prajjwalprajjwal/Click/firmware/src/applets/clicker/ClickerConfig.h

#ifndef CLICKER_CONFIG_H
#define CLICKER_CONFIG_H

#ifndef CLICKER_DEBUG
#define CLICKER_DEBUG 0
#endif

#define CLICKER_PERSIST_IDLE_DELAY_MS 1000
#define CLICKER_PERSIST_EVERY_N_CLICKS 20
#define CLICKER_PERSIST_MAX_INTERVAL_MS 0

#define CLICKER_NVS_NAMESPACE "clicker"
#define CLICKER_NVS_KEY_COUNT_STR "cnt_str"
#define CLICKER_NVS_KEY_TERRAIN_OFFSET "terrain_off"
#define CLICKER_NVS_KEY_LIFETIME_LO "lifetime_lo"
#define CLICKER_NVS_KEY_LIFETIME_HI "lifetime_hi"
#define CLICKER_NVS_KEY_COMPLETED_CYCLES "cycles"
#define CLICKER_NVS_KEY_MILESTONES "milestones"
#define CLICKER_NVS_KEY_HOME_UNLOCKS "home_unlocks"
#define CLICKER_NVS_KEY_LAST_CYCLE "last_cycle"
#define CLICKER_NVS_KEY_LAST_CYCLE_HI "last_cycle_hi"

#define CLICKER_CYCLE_LENGTH 100000ULL

#endif // CLICKER_CONFIG_H
