prajjwalprajjwal/Click/firmware/src/applets/clicker/SisyphusSprites.h

#ifndef SISYPHUS_SPRITES_H
#define SISYPHUS_SPRITES_H

#include <Arduino.h>

// Sprite Dimensions
#define SISYPHUS_IDLE_WIDTH 20
#define SISYPHUS_IDLE_HEIGHT 30

#define SISYPHUS_REST_WIDTH 26
#define SISYPHUS_REST_HEIGHT 27

#define SISYPHUS_PUSH_WIDTH 27
#define SISYPHUS_PUSH_HEIGHT 24

#define BOULDER_WIDTH 29
#define BOULDER_HEIGHT 29
#define BOULDER_FRAMES 5

#define DISTANT_MTN_WIDTH 64
#define DISTANT_MTN_HEIGHT 8

#define CLOUD1_WIDTH 16
#define CLOUD1_HEIGHT 6

#define CLOUD2_WIDTH 12
#define CLOUD2_HEIGHT 5

#define TERRAIN_MOUND_WIDTH 20
#define TERRAIN_MOUND_HEIGHT 12

#define TERRAIN_GRASS_WIDTH 10
#define TERRAIN_GRASS_HEIGHT 6

// boulder_frame_0_bmp: 29x29, 4 bytes/row, total 116 bytes
static const uint8_t boulder_frame_0_bmp[] PROGMEM = {
    0x00, 0xF8, 0xF8, 0x00, 0x03, 0xC1, 0x86, 0x00, 0x07, 0xA0, 0xC3, 0x00,
    0x0F, 0x60, 0xE3, 0x80, 0x1E, 0x00, 0x7B, 0xC0, 0x3E, 0x00, 0x18, 0x20,
    0x3C, 0x10, 0x00, 0x20, 0x78, 0x30, 0x08, 0x30, 0x60, 0x00, 0x1F, 0xD0,
    0xD0, 0x01, 0x87, 0xD8, 0xE0, 0x01, 0x87, 0x88, 0xC0, 0x01, 0x83, 0x88,
    0xC0, 0x00, 0xC3, 0x08, 0x80, 0x00, 0x43, 0x08, 0x80, 0x80, 0x43, 0x28,
    0xC8, 0x80, 0x42, 0x68, 0xD8, 0x80, 0x04, 0x58, 0x78, 0x80, 0x00, 0xD0,
    0x6C, 0x80, 0x00, 0x70, 0x64, 0x00, 0x00, 0xF0, 0x3A, 0x00, 0x0C, 0xE0,
    0x3C, 0x00, 0x00, 0xC0, 0x1E, 0x00, 0x80, 0x80, 0x0E, 0x00, 0x03, 0x80,
    0x02, 0x00, 0x0F, 0x00, 0x01, 0x80, 0x1C, 0x00, 0x00, 0x7F, 0xF8, 0x00,
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
    0x00, 0x08, 0x00, 0x30, 0x80, 0x06, 0x60, 0x00,
    0x00, 0x77, 0x00, 0xE0, 0xF0, 0x1E, 0x18, 0x00,
    0x00, 0xB1, 0xE1, 0x00, 0x4E, 0x68, 0x1F, 0x80,
    0x1F, 0x00, 0x1E, 0x00, 0x03, 0x80, 0x04, 0x7C,
    0xEC, 0x00, 0x0C, 0x00, 0x01, 0x00, 0x00, 0x32,
};

// cloud_wisp_1_bmp: 36x3, 5 bytes/row, total 15 bytes (thin tiered irregular cloud bar)
#define CLOUD_WISP_1_WIDTH 36
#define CLOUD_WISP_1_HEIGHT 3
static const uint8_t cloud_wisp_1_bmp[] PROGMEM = {
    0x00, 0x03, 0xF0, 0x00, 0x00,
    0x00, 0xFF, 0xF8, 0x3C, 0x00,
    0x7F, 0xFF, 0xFF, 0xFF, 0xF0,
};

// cloud_wisp_2_bmp: 36x3, 5 bytes/row, total 15 bytes (thin irregular broken streak wisp)
#define CLOUD_WISP_2_WIDTH 36
#define CLOUD_WISP_2_HEIGHT 3
static const uint8_t cloud_wisp_2_bmp[] PROGMEM = {
    0x0F, 0xFC, 0x01, 0xFC, 0x00,
    0x7F, 0xFF, 0x8F, 0xFF, 0x30,
    0x01, 0xF0, 0x00, 0x78, 0x00,
};

// cloud_wisp_3_bmp: 27x3, 4 bytes/row, total 12 bytes (thin delicate cirrus wisp)
#define CLOUD_WISP_3_WIDTH 27
#define CLOUD_WISP_3_HEIGHT 3
static const uint8_t cloud_wisp_3_bmp[] PROGMEM = {
    0x01, 0xE0, 0x00, 0x00,
    0x7F, 0xFE, 0x3F, 0x80,
    0x0F, 0xC0, 0x00, 0x00,
};

// terrain_mound_bmp: 20x12, 3 bytes/row, total 36 bytes
static const uint8_t terrain_mound_bmp[] PROGMEM = {
    0x0E, 0xFF, 0xF0, 0x0F, 0xFF, 0xB0, 0x9F, 0x80, 0x20, 0x00, 0x00, 0x00,
    0x00, 0x10, 0x00, 0x00, 0x60, 0x00, 0x00, 0xC0, 0x00, 0x01, 0x80, 0x00,
    0x01, 0x00, 0x00, 0x00, 0x00, 0x00, 0x00, 0x00, 0x00, 0x00, 0x00, 0x00,
};

// terrain_grass_bmp: 10x6, 2 bytes/row, total 12 bytes
static const uint8_t terrain_grass_bmp[] PROGMEM = {
    0x00, 0x00, 0x00, 0x00, 0x70, 0x00, 0xFF, 0xC0, 0xFE, 0x00, 0xC4, 0x00,
};

// bush_small_bmp: 8x5, 1 bytes/row, total 5 bytes
#define BUSH_SMALL_WIDTH 8
#define BUSH_SMALL_HEIGHT 5
static const uint8_t bush_small_bmp[] PROGMEM = {
    0x30, 0x78, 0xFC, 0x78, 0x30,
};

// bush_med_bmp: 12x6, 2 bytes/row, total 12 bytes
#define BUSH_MED_WIDTH 12
#define BUSH_MED_HEIGHT 6
static const uint8_t bush_med_bmp[] PROGMEM = {
    0x1E, 0x00, 0x3F, 0x00, 0xFF, 0xC0, 0xFF, 0xC0, 0x3F, 0x00, 0x1E, 0x00,
};

// rock_sm_bmp: 6x4, 1 bytes/row, total 4 bytes
#define ROCK_SM_WIDTH 6
#define ROCK_SM_HEIGHT 4
static const uint8_t rock_sm_bmp[] PROGMEM = {
    0x30,
    0xF8,
    0xF4,
    0x70,
};

// rock_round_bmp: 8x5, 1 bytes/row, total 5 bytes
#define ROCK_ROUND_WIDTH 8
#define ROCK_ROUND_HEIGHT 5
static const uint8_t rock_round_bmp[] PROGMEM = {
    0x3C, 0xCF, 0xFF, 0x7E, 0x3C,
};

// flower_bmp: 5x6, 1 bytes/row, total 6 bytes
#define FLOWER_WIDTH 5
#define FLOWER_HEIGHT 6
static const uint8_t flower_bmp[] PROGMEM = {
    0x50, 0x20, 0x50, 0x20, 0x20, 0x20,
};

// marker_post_bmp: 3x7, 1 bytes/row, total 7 bytes
#define MARKER_POST_WIDTH 3
#define MARKER_POST_HEIGHT 7
static const uint8_t marker_post_bmp[] PROGMEM = {
    0xE0, 0x40, 0xE0, 0x40, 0x40, 0x40, 0x40,
};

// tree_pine_bmp: 7x10, 1 bytes/row, total 10 bytes (small mountain pine tree)
#define TREE_PINE_WIDTH 7
#define TREE_PINE_HEIGHT 10
static const uint8_t tree_pine_bmp[] PROGMEM = {
    0x20, 0x70, 0xF8, 0x70, 0xF8, 0xFE, 0x70, 0xFE, 0x20, 0x20,
};

// stone_cluster_bmp: 8x4, 1 bytes/row, total 4 bytes (cluster of rocky stones)
#define STONE_CLUSTER_WIDTH 8
#define STONE_CLUSTER_HEIGHT 4
static const uint8_t stone_cluster_bmp[] PROGMEM = {
    0x64, 0xFE, 0xBF, 0xF6,
};


// hill_corner_profile: occupying ~30% of display in bottom-right corner (from
// x=38 to 127) Ridges, shelves, small ups & downs, overall uphill from y=63 at
// x=38 to y=37 at x=127
static const uint8_t hill_corner_profile[128] PROGMEM = {
    64, 64, 64, 64, 64, 64, 64, 64, 64, 64, 64, 64, 64, 64, 64, 64, 64, 64, 64,
    64, 64, 64, 64, 64, 64, 64, 64, 64, 64, 64, 64, 64, 64, 64, 64, 64, 64, 64,
    63, 63, 63, 63, 63, 63, 63, 63, 62, 62, 60, 59, 59, 59, 58, 58, 59, 59, 59,
    59, 58, 58, 58, 57, 57, 56, 54, 53, 53, 52, 51, 51, 52, 51, 51, 50, 50, 50,
    50, 50, 50, 50, 49, 49, 49, 49, 49, 50, 51, 51, 51, 50, 50, 49, 49, 48, 48,
    47, 45, 44, 44, 43, 43, 42, 44, 43, 43, 43, 42, 42, 42, 42, 41, 41, 39, 39,
    38, 38, 37, 37, 38, 37, 37, 37, 37, 36, 36, 36, 37, 37,
};

#endif // SISYPHUS_SPRITES_H
