prajjwalprajjwal/Click/firmware/src/system/OSManager.h

#ifndef OS_MANAGER_H
#define OS_MANAGER_H

#include <Arduino.h>
#include "Applet.h"
#include "InputManager.h"

class OSManager {
public:
    enum SleepState {
        AWAKE,
        LIGHT_SLEEP,
        DEEP_SLEEP
    };

private:
    static constexpr uint8_t MAX_APPLETS = 8;  // supports up to 8 registered applets
    Applet* applets[MAX_APPLETS] = {nullptr};
    uint8_t appletCount = 0;
    uint8_t currentAppletIndex = 0;
    Applet* currentApplet = nullptr;
    Applet* screensaverApplet = nullptr;
    InputManager inputManager;
    
    // Sleep management
    SleepState sleepState = AWAKE;
    uint32_t lastActivityTime = 0;
    uint32_t firstWakeClickTime = 0;
    uint8_t firstWakeClickButton = 0;      // 1 = MODE, 2 = ACTION
    uint32_t lightSleepTimeout = 15000;    // 15 seconds before display off
    uint32_t deepSleepTimeout = 30000;     // 30 seconds before deep sleep
    bool displayOn = true;
    bool isDimmed = false;

public:
    OSManager();
    void init();
    void update();
    void draw();
    
    void registerApplet(Applet* applet);
    void setScreensaverApplet(Applet* applet) { screensaverApplet = applet; }
    Applet* getScreensaverApplet() const { return screensaverApplet; }
    void switchToApplet(uint8_t index);
    void switchToNextApplet();
    uint8_t getCurrentAppletIndex() const { return currentAppletIndex; }
    Applet* getCurrentApplet() { return currentApplet; }
    InputManager* getInputManager() { return &inputManager; }
    
    // Sleep/wake functions
    bool recordActivity(uint8_t button = 0);
    void enterLightSleep();
    void wakeFromLightSleep();
    void enterDeepSleep();
    SleepState getSleepState() const { return sleepState; }
    bool isDisplayOn() const { return displayOn; }
    void setLightSleepTimeout(uint32_t ms) { lightSleepTimeout = ms; }
    void setDeepSleepTimeout(uint32_t ms) { deepSleepTimeout = ms; }

private:
    void checkSleepConditions();
};

#endif // OS_MANAGER_H
