prajjwalprajjwal/Click/firmware/src/applets/clicker/CounterRenderer.h

#ifndef COUNTER_RENDERER_H
#define COUNTER_RENDERER_H

#include "SisyphusSprites.h"
#include <Arduino.h>
#include <stddef.h>
#include <stdint.h>

class CounterRenderer {
private:
  void formatDisplayCount(const char *countStr, char *buffer,
                          size_t bufferSize) const;
  void drawBackground(float worldProgress, int32_t climbProgress,
                      int16_t charX) const;
  void drawHillTerrain(int32_t hillOffset, int32_t climbProgress) const;
  void drawBoulder(int16_t bx, int16_t by, uint8_t rotFrame) const;
  void drawSisyphus(int16_t sx, int16_t sy, const uint8_t *spriteBmp,
                    uint8_t width, uint8_t height) const;
  void drawCounterText(const char *countStr) const;

public:
  // Ground profile:
  // - Hill occupies ~30% in bottom-right corner (from x=38 to 127) with ridges
  // and shelves, overall uphill.
  // - On left (x < 38): starts with flat ground plane at y=62, which moves
  // downwards out of frame when movement starts.
  static inline int16_t getSlopeGroundY(int16_t x, int32_t climbProgress) {
    if (x >= 38) {
      if (x > 127)
        x = 127;
      return pgm_read_byte(&hill_corner_profile[x]);
    } else {
      if (climbProgress > 30) {
        return 100; // Flat plane has cleanly moved below the screen
      }
      if (climbProgress > 18) {
        return 62 + static_cast<int16_t>(climbProgress - 18) * 3;
      }
      return 62; // Solid flat plain ground while character approaches slope
    }
  }

  void renderScene(const char *countStr, const uint8_t *sisyphusSprite,
                   uint8_t sisyphusWidth, uint8_t sisyphusHeight, int16_t charX,
                   int16_t bldX, uint8_t boulderRotFrame, int32_t hillOffset,
                   float worldProgress, int32_t climbProgress);
};

#endif // COUNTER_RENDERER_H
