prajjwalprajjwal/Click/firmware/src/applets/clicker/PersistenceManager.h

#ifndef PERSISTENCE_MANAGER_H
#define PERSISTENCE_MANAGER_H

#include <Arduino.h>
#include <Preferences.h>
#include <stdint.h>
#include "ClickCounter.h"
#include "MilestoneTypes.h"

class PersistenceManager {
private:
    Preferences prefs;
    bool dirty = false;
    uint32_t clicksSincePersist = 0;
    uint32_t homeUnlockFlags = 0;
    uint64_t lastCycleCompleteLifetime = 0;
    uint32_t lastClickTime = 0;
    uint32_t lastPersistTime = 0;
    uint32_t terrainOffset = 0;
    // Cached values to avoid redundant SPI flash writes
    uint32_t lastSavedTerrainOffset = UINT32_MAX;
    uint32_t lastSavedHomeUnlocks = UINT32_MAX;
    uint64_t lastSavedLastCycle = UINT64_MAX;
    uint32_t lastSavedMilestones[MILESTONE_FLAG_WORDS] = {0};
    char lastSavedCountStr[ClickCounter::MAX_DIGITS] = {0};

    bool save(const ClickCounter& counter, const uint32_t milestoneFlags[MILESTONE_FLAG_WORDS]);

public:
    bool begin();
    bool load(ClickCounter& counter, uint32_t milestoneFlags[MILESTONE_FLAG_WORDS]);
    bool flush(const ClickCounter& counter, const uint32_t milestoneFlags[MILESTONE_FLAG_WORDS]);

    void markDirty(uint32_t now = 0);
    void onClickRecorded(uint32_t now);
    bool shouldPersist(uint32_t now) const;
    void clearPeriodicCounter();

    bool isDirty() const { return dirty; }

    uint32_t getTerrainOffset() const { return terrainOffset; }
    void setTerrainOffset(uint32_t off) {
        if (terrainOffset != off) {
            terrainOffset = off;
            dirty = true;
        }
    }

    uint32_t getHomeUnlockFlags() const { return homeUnlockFlags; }
    void setHomeUnlockFlags(uint32_t flags) {
        if (homeUnlockFlags != flags) {
            homeUnlockFlags = flags;
            dirty = true;
        }
    }

    uint64_t getLastCycleCompleteLifetime() const { return lastCycleCompleteLifetime; }
    void setLastCycleCompleteLifetime(uint64_t value) {
        if (lastCycleCompleteLifetime != value) {
            lastCycleCompleteLifetime = value;
            dirty = true;
        }
    }
};

#endif // PERSISTENCE_MANAGER_H
